Karthik-v202/Design-and-Finite-Element-Analysis-of-a-Rigid-Steel-Portal-Frame/Assets/Screenshot 2025-11-29 070858.png

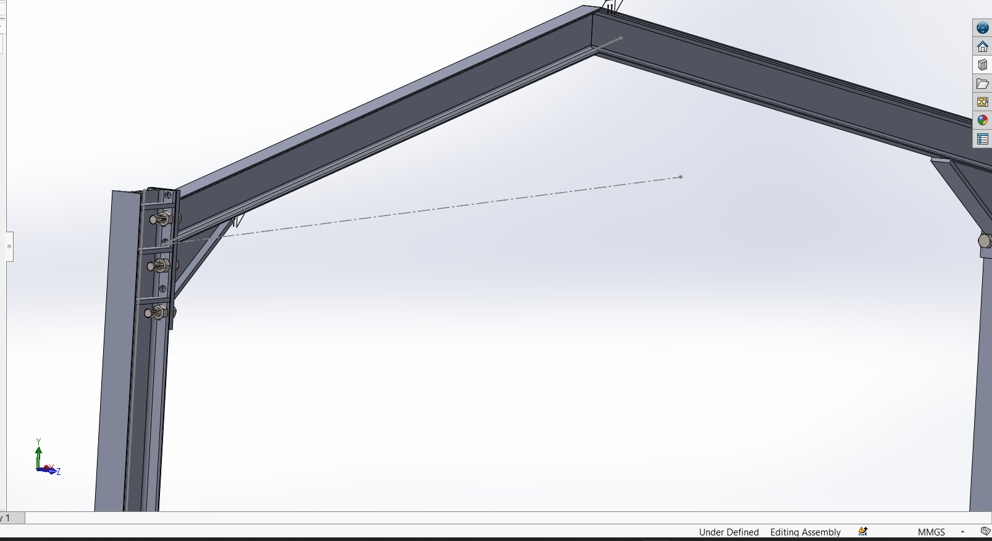
Assets/Screenshot 2025-11-29 070858.png
