Karthik-v202/Design-and-Finite-Element-Analysis-of-a-Rigid-Steel-Portal-Frame/Assets/Screenshot 2025-12-01 212748.png

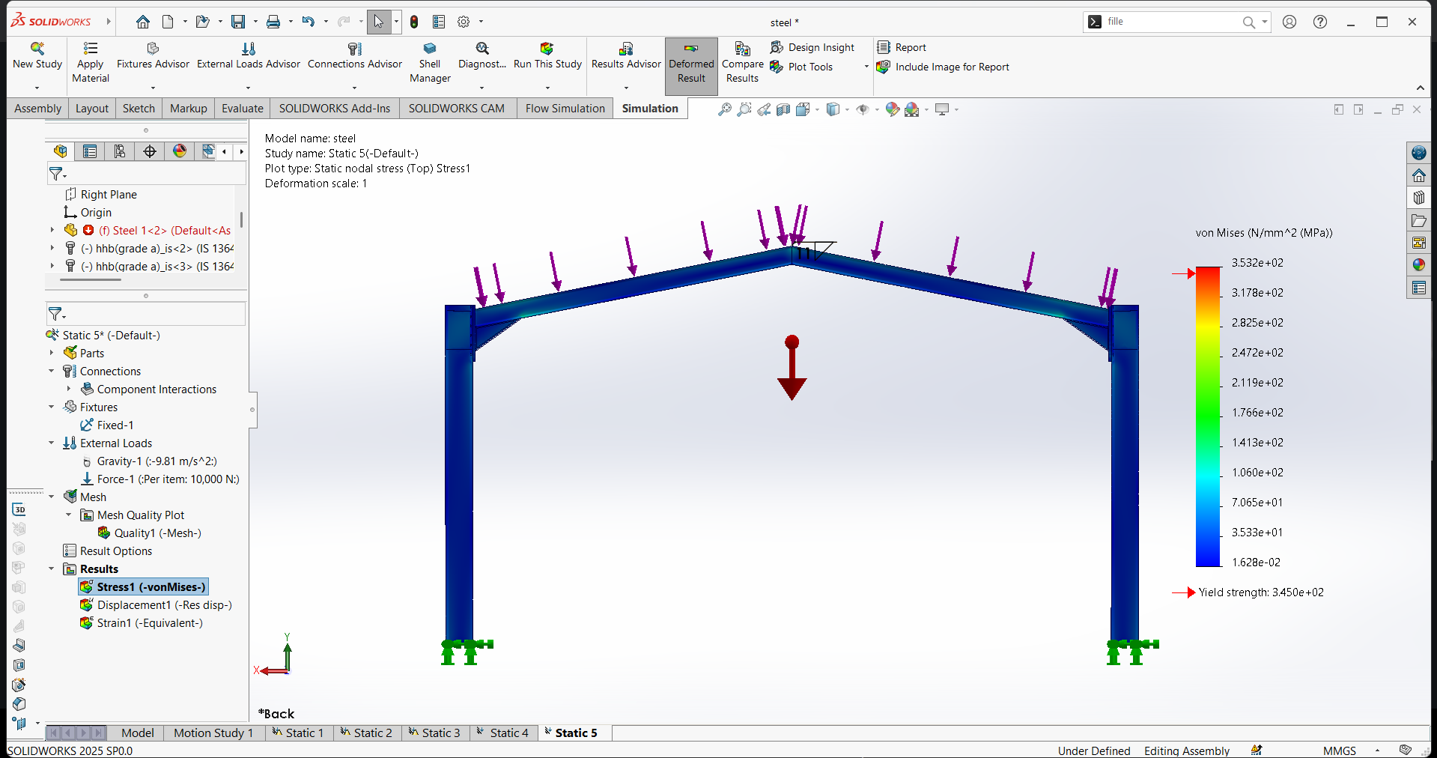
Assets/Screenshot 2025-12-01 212748.png
